Shong16-cyber/512B_Assignment_4/Documentation/SuzyH_512B_SchematicDesign/SuzyH_512B_SchematicDesign.kicad_sch

## KiCad design Documentation/SuzyH_512B_SchematicDesign/SuzyH_512B_SchematicDesign.kicad_sch (2025-12-10)

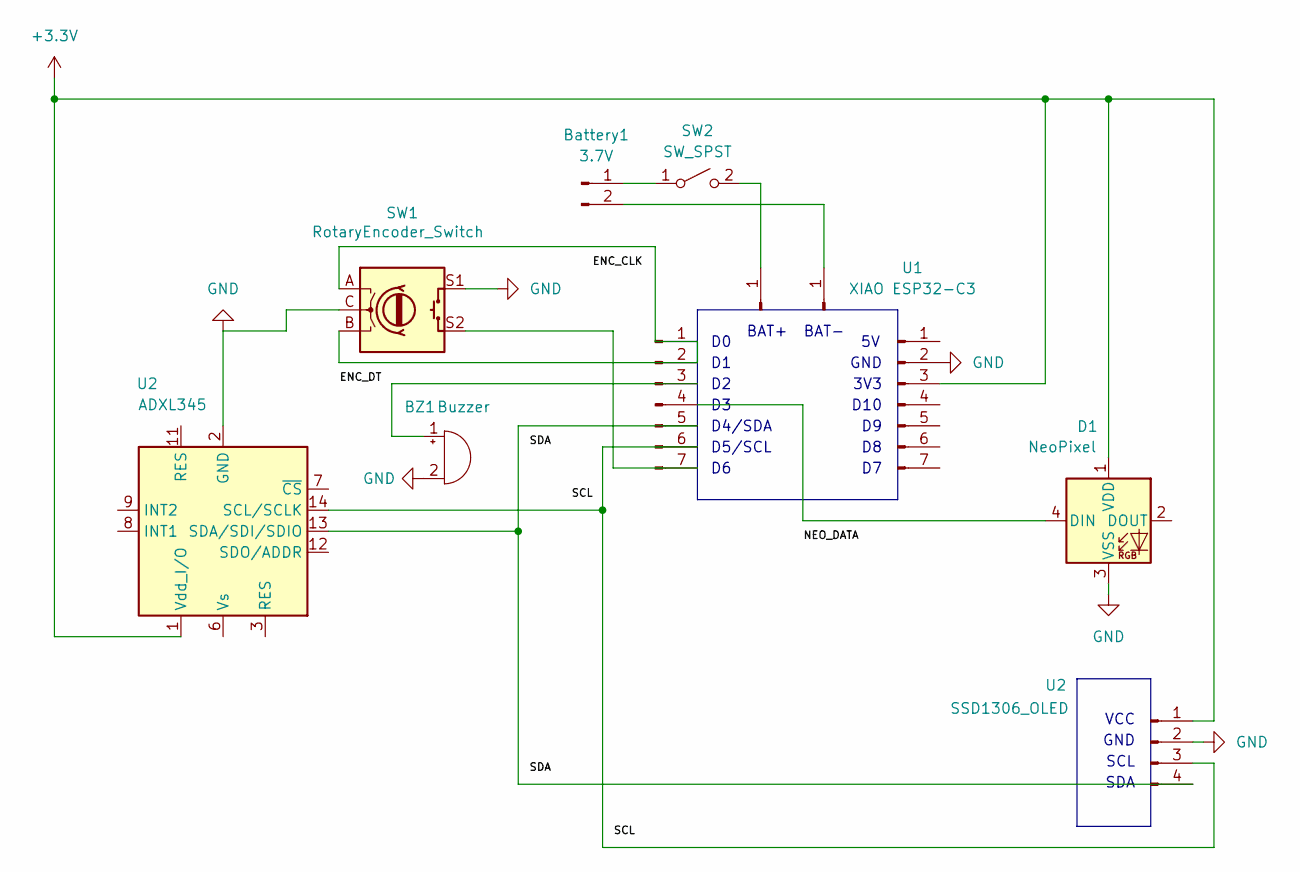
[picture p3: schematic SuzyH_512B_SchematicDesign.kicad_sch]

Parts:
BZ1: Buzzer
Battery1: 3.7V; Battery
D1: NeoPixel; LED_WS2812B_PLCC4_5.0x5.0mm_P3.2mm
J1, J2: Conn_01x01_Pin
SW1: RotaryEncoder_Switch
SW2: SW_SPST
U1: XIAO ESP32-C3
U2: SSD1306_OLED

Connections:
+3.3V: D1.1 (VDD), U1.3, U2.1 (Vdd_I/O)
GND: BZ1.2 (-), D1.3 (VSS), SW1.C, SW1.S1, U1.2, U2.2 (GND), U2.4 (GND), U2.5 (GND)
unnamed: BZ1.1 (+), U1.3
unnamed: Battery1.1, SW2.1 (A)
unnamed: Battery1.2, J2.1
unnamed: D1.4 (DIN), U1.4
unnamed: J1.1, SW2.2 (B)
unnamed: SW1.A, SW1.B, U1.1, U1.2
unnamed: SW1.S2, U1.7
unnamed: U1.5, U2.4 (GND), U2.13 (SDA/SDI/SDIO)
unnamed: U1.6, U2.3 (RES), U2.14 (SCL/SCLK)

Notes on the sheet:
GND
D4/SDA
3V3
D10
D5/SCL
VCC
SDA
SCL
BAT+
BAT-
